ohmbase/mix-g1-3dprinter/base-top-2_pp.stl

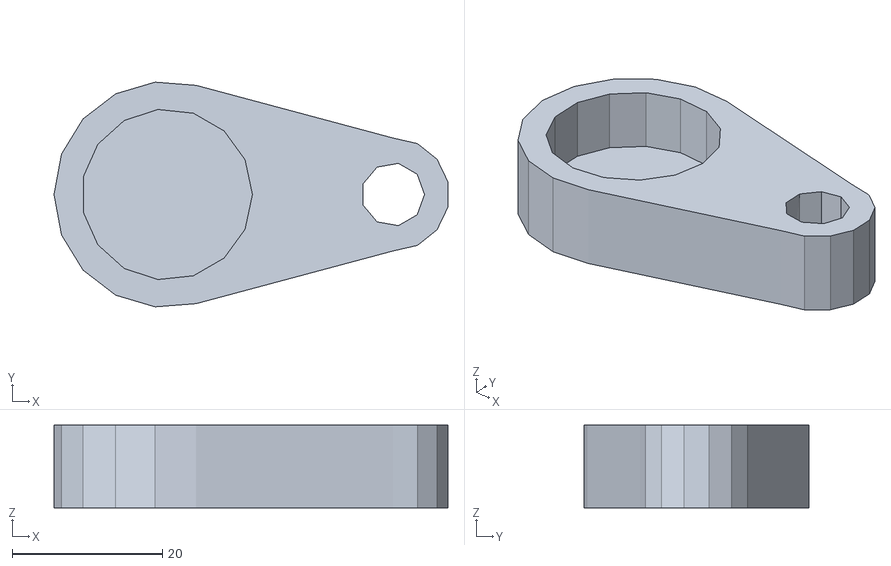
[picture p15: CAD file, 2015-05-13]
base-top-2_pp.stl
52.5 x 30.0 x 11.0
