ohmbase/mix-g1-3dprinter/y-motor-holder_pp.stl

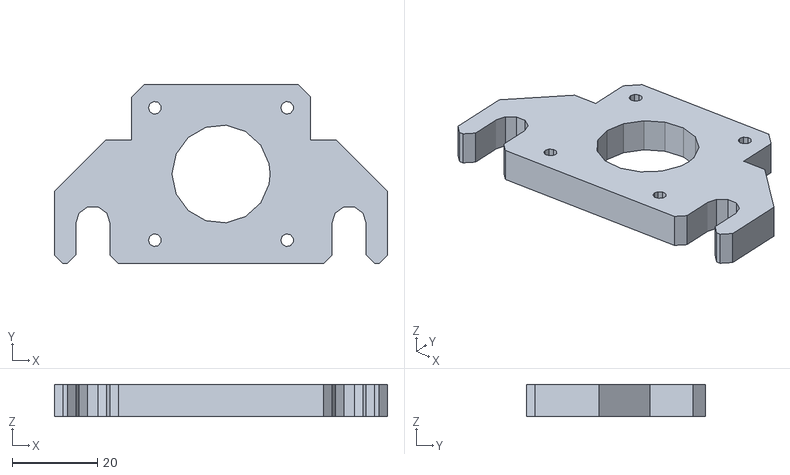
[picture p16: CAD file, 2015-05-13]
y-motor-holder_pp.stl
78.3 x 42.2 x 7.53
