ohmbase/mix-g1-3dprinter/power-supply-hook-pp.stl

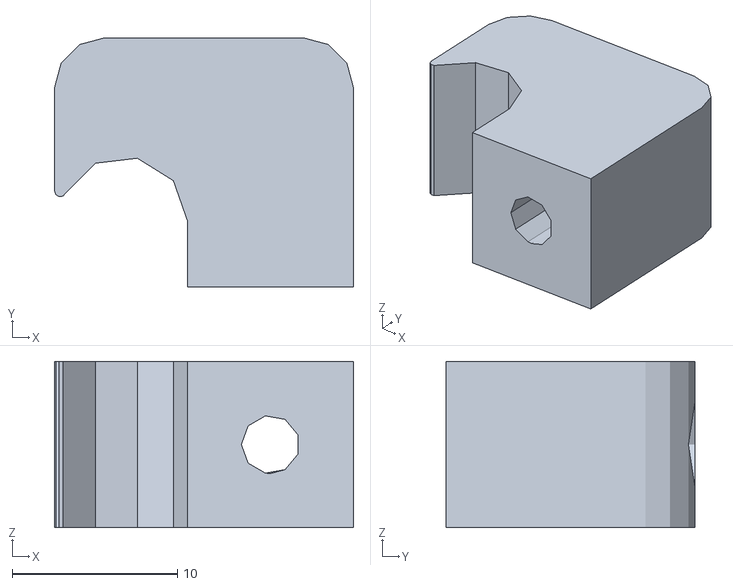
[picture p17: CAD file, 2015-05-13]
power-supply-hook-pp.stl
18.1 x 15.1 x 10.0
