ohmbase/mix-g1-3dprinter/x-motor-holder-2-pp.stl

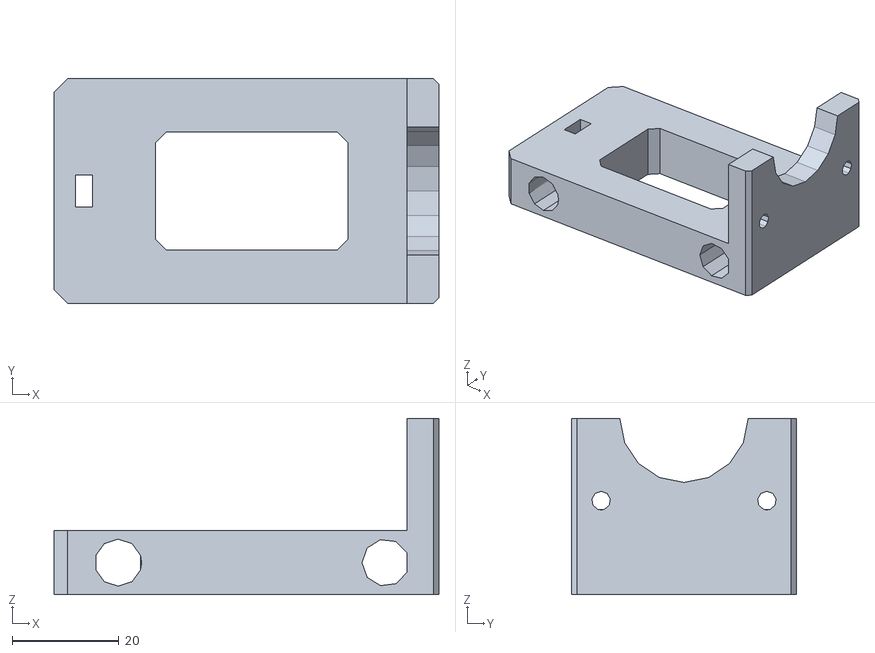
[picture p18: CAD file, 2015-05-13]
x-motor-holder-2-pp.stl
72.3 x 42.2 x 33.1
