ohmbase/mix-g1-3dprinter/pulley.stl

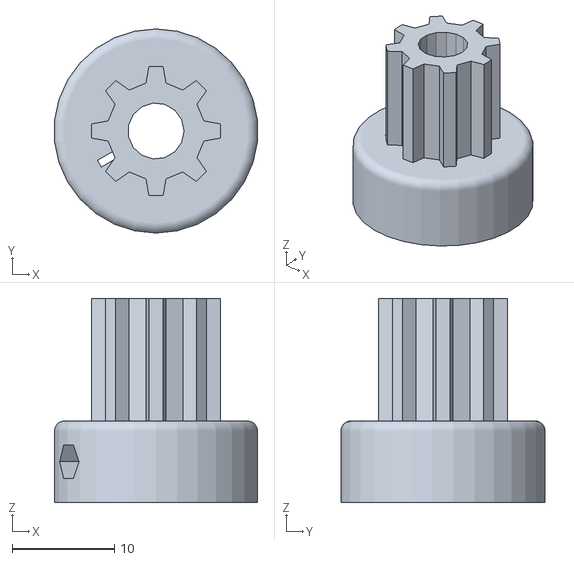
[picture p19: CAD file, 2015-05-13]
pulley.stl
19.9 x 20.0 x 20.0
