ohmbase/mix-g1-3dprinter/base_part_1_pp.stl

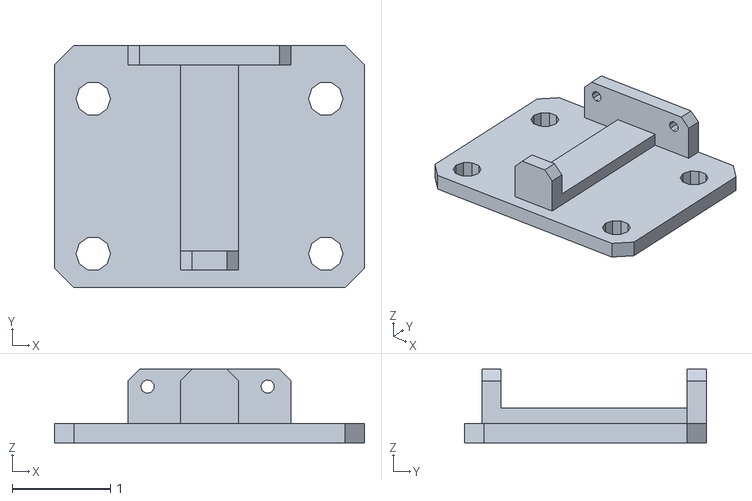
[picture p20: CAD file, 2015-05-13]
base_part_1_pp.stl
3.15 x 2.46 x 0.748
